aidanjenkins2016/ME499/Test Images/20170127_183551.jpg

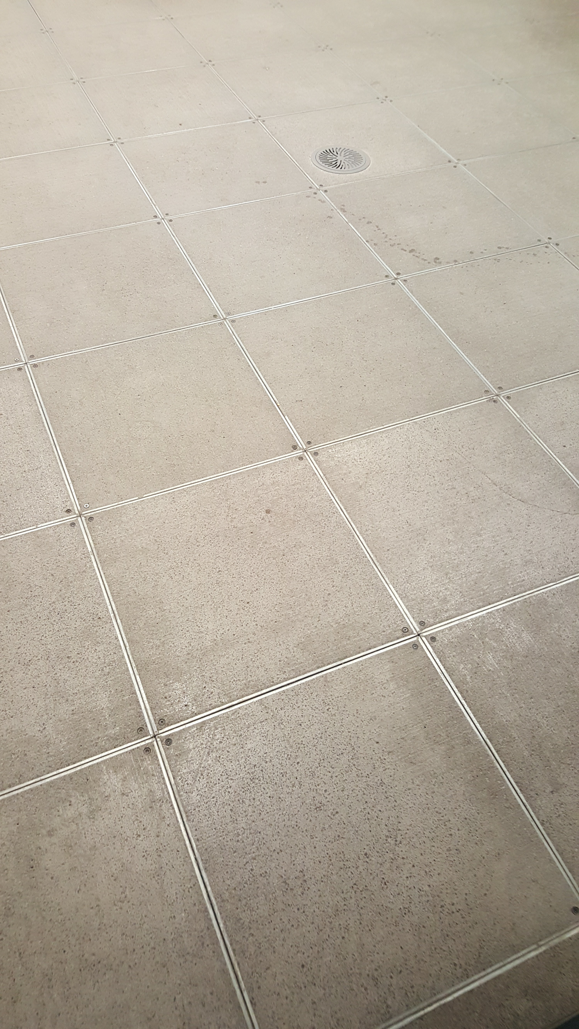
Test Images/20170127_183551.jpg
